niyikes/eiko-cam/Images/3.png

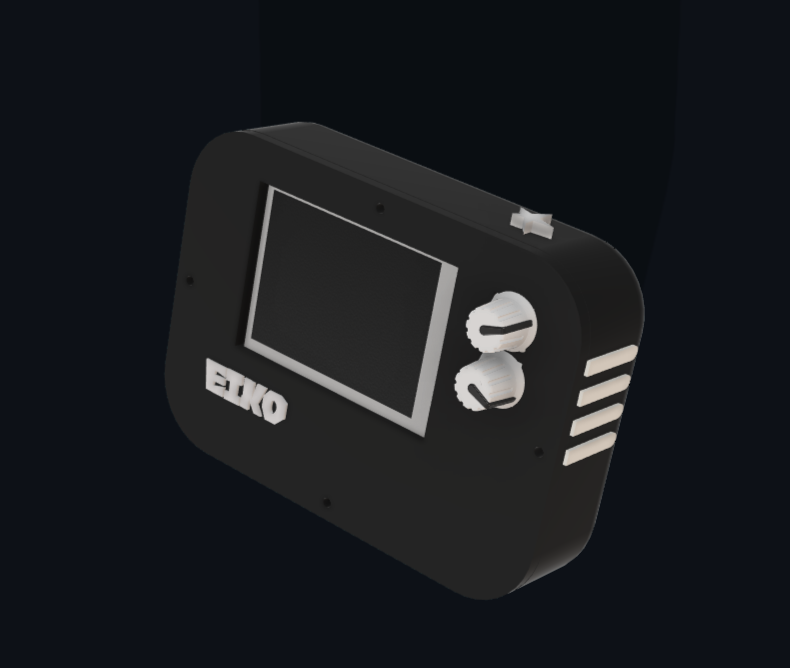
Images/3.png
